SpeechlessPanda/EnvironmentalMonitoringInstrument/assets/boot-animation/1.png

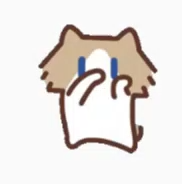
assets/boot-animation/1.png
