SpeechlessPanda/EnvironmentalMonitoringInstrument/assets/boot-animation/2.png

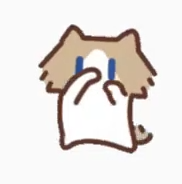
assets/boot-animation/2.png
