SpeechlessPanda/EnvironmentalMonitoringInstrument/assets/boot-animation/3.png

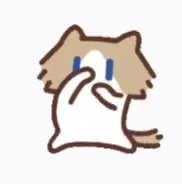
assets/boot-animation/3.png
