SpeechlessPanda/EnvironmentalMonitoringInstrument/assets/boot-animation/4.png

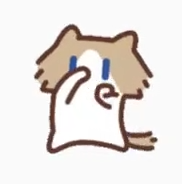
assets/boot-animation/4.png
