SpeechlessPanda/EnvironmentalMonitoringInstrument/assets/boot-animation/5.png

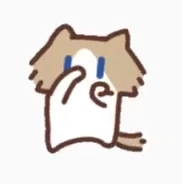
assets/boot-animation/5.png
