SpeechlessPanda/EnvironmentalMonitoringInstrument/assets/boot-animation/7.png

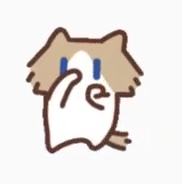
assets/boot-animation/7.png
