SpeechlessPanda/EnvironmentalMonitoringInstrument/assets/boot-animation/9.png

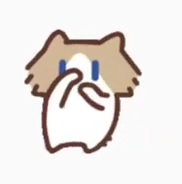
assets/boot-animation/9.png
