SpeechlessPanda/EnvironmentalMonitoringInstrument/assets/boot-animation/11.png

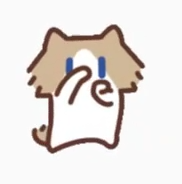
assets/boot-animation/11.png
