SpeechlessPanda/EnvironmentalMonitoringInstrument/assets/boot-animation/12.png

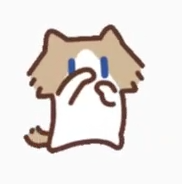
assets/boot-animation/12.png
