SpeechlessPanda/EnvironmentalMonitoringInstrument/firmware/BSP/png.c

#include "board.h"
#include <stdio.h>
#include "oled.h"
uint8_t MIAO1[] =
{0x00,0x00,0x00,0x00,0x00,0x00,0x00,0x00,0x00,0x00,0x00,0x00,0x00,0x00,0x00,0x00,
0x00,0x00,0x00,0x00,0x00,0x00,0x00,0x00,0x00,0x00,0x00,0x00,0x00,0x00,0x00,0x00,
0x00,0x00,0x00,0x00,0x00,0x00,0x00,0x00,0x00,0x00,0x00,0x00,0x00,0x00,0x00,0x00,
0x00,0x00,0x00,0x00,0x00,0x00,0x00,0x00,0x00,0x00,0x00,0x00,0x00,0x00,0x00,0x00,
0x00,0x00,0x00,0x00,0x00,0x00,0x00,0x00,0x00,0x00,0x00,0x00,0x00,0x00,0x00,0x00,
0x00,0x00,0x00,0x80,0xF8,0x0E,0x06,0x02,0x06,0x0C,0x1C,0x30,0x30,0x30,0x30,0x30,
0x30,0x30,0x30,0x30,0x30,0x30,0x20,0x30,0x30,0x18,0x0C,0x04,0x0C,0x3C,0xF0,0x00,
0x00,0x00,0x00,0x00,0x00,0x00,0x00,0x00,0x00,0x00,0x00,0x00,0x00,0x00,0x00,0x00,
0x00,0x00,0x00,0x00,0x00,0x00,0x00,0x00,0x00,0x00,0x00,0x80,0xC0,0x70,0x38,0x1C,
0x06,0x03,0x01,0x00,0x00,0x00,0x00,0x00,0x00,0xF0,0xF0,0x00,0x00,0x00,0x00,0x00,
0x00,0x00,0x00,0x00,0xE0,0xF0,0x00,0x00,0x00,0x00,0x00,0x00,0x00,0x03,0x07,0x1C,
0x38,0x70,0xC0,0x80,0x00,0x00,0x00,0x00,0x00,0x00,0x00,0x00,0x00,0x00,0x00,0x00,
0x00,0x00,0x00,0x00,0x00,0x00,0x00,0x00,0x00,0x00,0x00,0x04,0x0E,0xC2,0xF0,0x80,
0x80,0x80,0x80,0x00,0x00,0xC0,0x70,0x38,0x0F,0x0F,0x06,0x82,0xE3,0x73,0x31,0x19,
0x0F,0x00,0x00,0xC3,0xFF,0x0C,0x0C,0x04,0xC4,0xFC,0x38,0x00,0x00,0x00,0xC0,0xC0,
0x0C,0x3C,0x31,0x00,0x00,0x00,0x00,0x00,0x00,0x00,0x00,0x00,0x00,0x00,0x00,0x00,
0x00,0x00,0x00,0x00,0x00,0x00,0x00,0x00,0x00,0x00,0x00,0x00,0x00,0x00,0x00,0x00,
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
	OLED_ShowPicture(32,0,63,64,MIAO9,1);
	OLED_Refresh();
	delay_ms(83);
	OLED_ShowPicture(32,0,63,64,MIAO10,1);
	OLED_Refresh();
	delay_ms(83);
	OLED_ShowPicture(32,0,63,64,MIAO11,1);
	OLED_Refresh();
	delay_ms(83);
	OLED_ShowPicture(32,0,63,64,MIAO12,1);
	OLED_Refresh();
	delay_ms(83);
}
