SpeechlessPanda/EnvironmentalMonitoringInstrument/firmware/BSP/bsp_bmp180.h

/*
 * 立创开发板软硬件资料与相关扩展板软硬件资料官网全部开源
 * 开发板官网：www.lckfb.com
 * 技术支持常驻论坛，任何技术问题欢迎随时交流学习
 * 立创论坛：https://oshwhub.com/forum
 * 关注bilibili账号：【立创开发板】，掌握我们的最新动态！
 * 不靠卖板赚钱，以培养中国工程师为己任
 * Change Logs:
 * Date           Author       Notes
 * 2024-07-02     LCKFB-LP    first version
 */

#ifndef _BSP_BMP180_H_
#define _BSP_BMP180_H_

#include "board.h"


//设置SDA输出模式
#define SDA_OUT()   {                                                  \
                        DL_GPIO_initDigitalOutput(GPIO_SDA_IOMUX);     \
                        DL_GPIO_setPins(GPIO_PORT, GPIO_SDA_PIN);      \
                        DL_GPIO_enableOutput(GPIO_PORT, GPIO_SDA_PIN); \
                    }
//设置SDA输入模式
#define SDA_IN()    { DL_GPIO_initDigitalInput(GPIO_SDA_IOMUX); }
//获取SDA引脚的电平变化
#define SDA_GET()   ( ( ( DL_GPIO_readPins(GPIO_PORT,GPIO_SDA_PIN) & GPIO_SDA_PIN ) > 0 ) ? 1 : 0 )
//SDA与SCL输出
#define SDA(x)      ( (x) ? (DL_GPIO_setPins(GPIO_PORT,GPIO_SDA_PIN)) : (DL_GPIO_clearPins(GPIO_PORT,GPIO_SDA_PIN)) )
#define SCL(x)      ( (x) ? (DL_GPIO_setPins(GPIO_PORT,GPIO_SCL_PIN)) : (DL_GPIO_clearPins(GPIO_PORT,GPIO_SCL_PIN)) )


float BMP180_Get_Temperature(void);
float BMP180_Get_Pressure(void);
void BMP180_Write_Cmd(uint8_t regaddr,uint8_t cmd);
void BMP180_Get_param(void);
float BMP180_Get_Altitude(float p);
void BMP180_Disable(void);
void BMP180_Init(void);
	
// 把这些声明加入到 bsp_bmp180.h 中，用来向其他文件公开 I2C 接口
void IIC_Start(void);
void IIC_Stop(void);
void IIC_Send_Ack(unsigned char ack);
unsigned char I2C_WaitAck(void);
void Send_Byte(uint8_t dat);
unsigned char Read_Byte(void);
#endif
