SpeechlessPanda/EnvironmentalMonitoringInstrument/firmware/board.c

/*
 * 立创开发板软硬件资料与相关扩展板软硬件资料官网全部开源
 * 开发板官网：www.lckfb.com
 * 技术支持常驻论坛，任何技术问题欢迎随时交流学习
 * 立创论坛：https://oshwhub.com/forum
 * 关注bilibili账号：【立创开发板】，掌握我们的最新动态！
 * 不靠卖板赚钱，以培养中国工程师为己任
 * Change Logs:
 * Date           Author       Notes
 * 2024-06-26     LCKFB     first version
 */
#include "board.h"
#include "stdio.h"

#define RE_0_BUFF_LEN_MAX	128

volatile uint8_t  recv0_buff[RE_0_BUFF_LEN_MAX] = {0};
volatile uint16_t recv0_length = 0;
volatile uint8_t  recv0_flag = 0;

void board_init(void)
{
	// SYSCFG初始化
	SYSCFG_DL_init();
	//清除串口中断标志
	NVIC_ClearPendingIRQ(UART_0_INST_INT_IRQN);
	//使能串口中断
	NVIC_EnableIRQ(UART_0_INST_INT_IRQN);
	
	printf("Board Init [[ ** LCKFB ** ]]\r\n");
}

//搭配滴答定时器实现的精确us延时
void delay_us(unsigned long __us) 
{
    uint32_t ticks;
    uint32_t told, tnow, tcnt = 38;

    // 计算需要的时钟数 = 延迟微秒数 * 每微秒的时钟数
    ticks = __us * (32000000 / 1000000);

    // 获取当前的SysTick值
    told = SysTick->VAL;

    while (1)
    {
        // 重复刷新获取当前的SysTick值
        tnow = SysTick->VAL;

        if (tnow != told)
        {
            if (tnow < told)
                tcnt += told - tnow;
            else
                tcnt += SysTick->LOAD - tnow + told;

            told = tnow;

            // 如果达到了需要的时钟数，就退出循环
            if (tcnt >= ticks)
                break;
        }
    }
}
//搭配滴答定时器实现的精确ms延时
void delay_ms(unsigned long ms) 
{
	delay_us( ms * 1000 );
}

void delay_1us(unsigned long __us){ delay_us(__us); }
void delay_1ms(unsigned long ms){ delay_ms(ms); }

//串口发送单个字符
void uart0_send_char(char ch)
{
	//当串口0忙的时候等待，不忙的时候再发送传进来的字符
	while( DL_UART_isBusy(UART_0_INST) == true );
	//发送单个字符
	DL_UART_Main_transmitData(UART_0_INST, ch);

}
//串口发送字符串
void uart0_send_string(char* str)
{
	//当前字符串地址不在结尾 并且 字符串首地址不为空
	while(*str!=0&&str!=0)
	{
		//发送字符串首地址中的字符，并且在发送完成之后首地址自增
		uart0_send_char(*str++);
	}
}


#if !defined(__MICROLIB)
//不使用微库的话就需要添加下面的函数
#if (__ARMCLIB_VERSION <= 6000000)
//如果编译器是AC5  就定义下面这个结构体
struct __FILE
{
	int handle;
};
#endif

FILE __stdout;

//定义_sys_exit()以避免使用半主机模式
void _sys_exit(int x)
{
	x = x;
}
#endif


//printf函数重定义
int fputc(int ch, FILE *stream)
{
	//当串口0忙的时候等待，不忙的时候再发送传进来的字符
	while( DL_UART_isBusy(UART_0_INST) == true );
	
	DL_UART_Main_transmitData(UART_0_INST, ch);
	
	return ch;
}

//串口的中断服务函数
void UART_0_INST_IRQHandler(void)
{
	uint8_t receivedData = 0;
	
	//如果产生了串口中断
	switch( DL_UART_getPendingInterrupt(UART_0_INST) )
	{
		case DL_UART_IIDX_RX://如果是接收中断
			
			// 接收发送过来的数据保存
			receivedData = DL_UART_Main_receiveData(UART_0_INST);

			// 检查缓冲区是否已满
			if (recv0_length < RE_0_BUFF_LEN_MAX - 1)
			{
				recv0_buff[recv0_length++] = receivedData;

				// 将保存的数据再发送出去，不想回传可以注释掉
				uart0_send_char(receivedData);
			}
			else
			{
				recv0_length = 0;
			}

			// 标记接收标志
			recv0_flag = 1;
		
			break;
		
		default://其他的串口中断
			break;
	}
}
